marconett/ha-dorbell/sender/sender.kicad_sch

## KiCad design sender/sender.kicad_sch (2026-07-05)

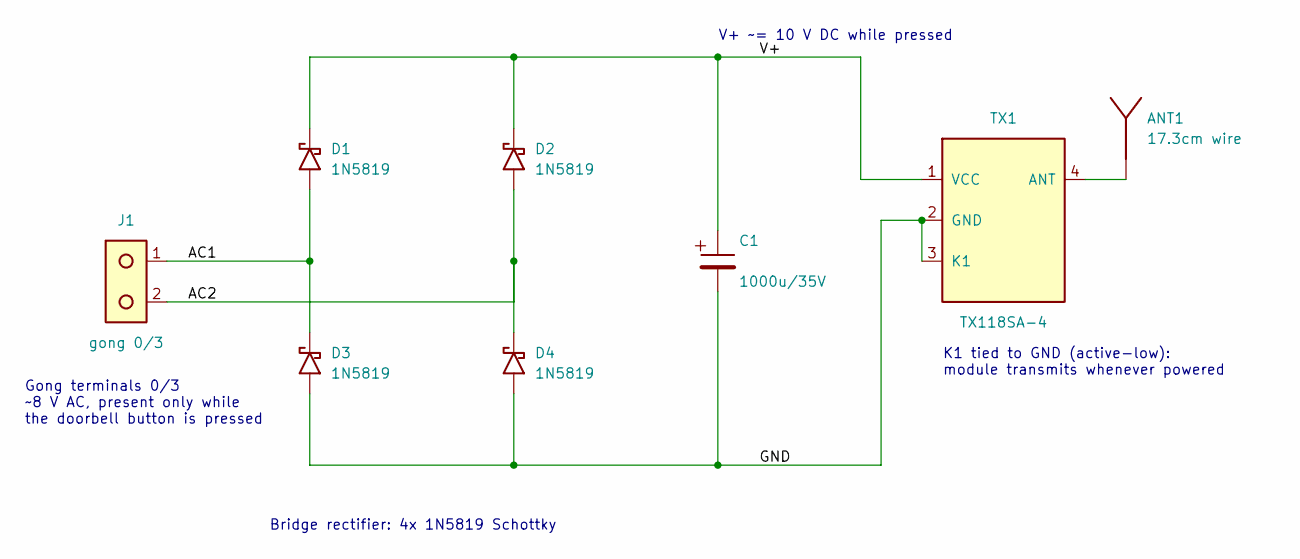
[picture p8: schematic sender.kicad_sch]

Parts:
ANT1: 17.3cm wire
C1: 1000u/35V
D1, D2, D3, D4: 1N5819
J1: gong 0/3
TX1: TX118SA-4

Connections:
AC1: D1.2 (A), D3.1 (K), J1.1 (AC1)
AC2: D2.2 (A), D4.1 (K), J1.2 (AC2)
GND: C1.2 (-), D3.2 (A), D4.2 (A), TX1.2 (GND), TX1.3 (K1)
unnamed: ANT1.1, TX1.4 (ANT)
V+: C1.1 (+), D1.1 (K), D2.1 (K), TX1.1 (VCC)

Notes on the sheet:
Gong terminals 0/3 ~8 V AC, present only while the doorbell button is pressed
Bridge rectifier: 4x 1N5819 Schottky
V+ ~= 10 V DC while pressed
K1 tied to GND (active-low): module transmits whenever powered
